FPGA-Computer/LED-Clock/Common anode/alarm clock.jpg

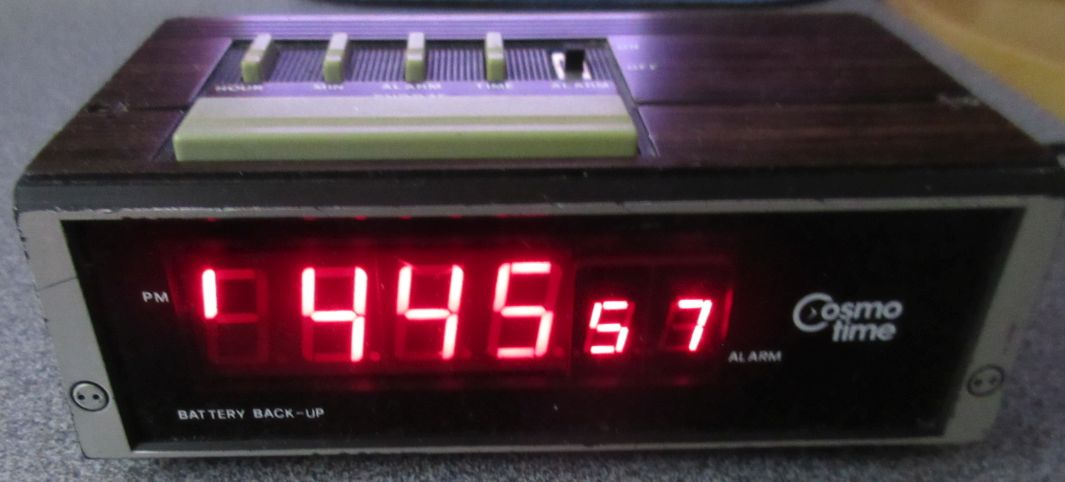
Common anode/alarm clock.jpg
