FPGA-Computer/LED-Clock/Common anode/Alarm setting.jpg

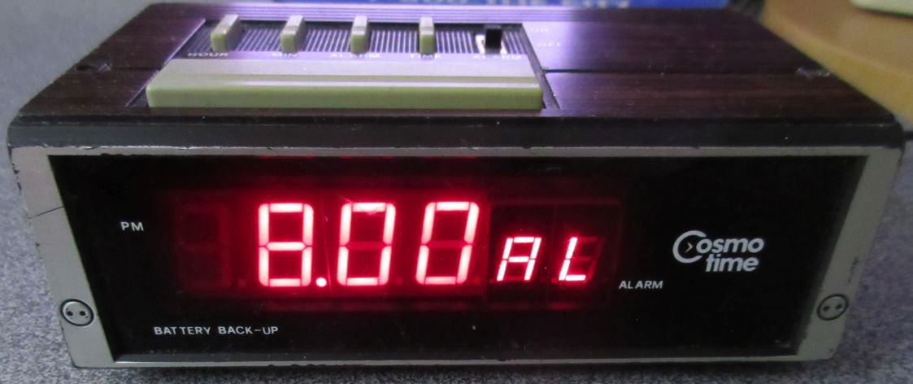
Common anode/Alarm setting.jpg
