FPGA-Computer/LED-Clock/Common anode/uC breakout + display PCB + Supercap backup.jpg

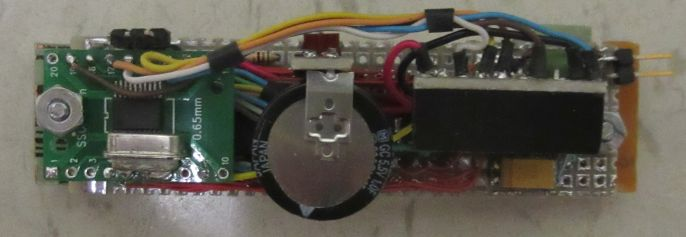
Common anode/uC breakout + display PCB + Supercap backup.jpg
