FPGA-Computer/LED-Clock/Common cathode/clock.jpg

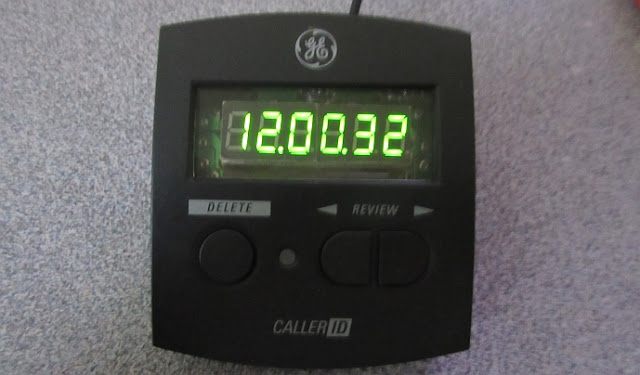
Common cathode/clock.jpg
